bad-alloc-heavy-industries/SPIFlashProgrammer/firmware/TivaC/Startup.c

/*
 * This file is part of SPI Flash Programmer (SPIFP)
 * Copyright © 2014 Rachel Mant (dx-mon@users.sourceforge.net)
 *
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
 * You should have received a copy of the GNU General Public License
 * along with this program.  If not, see <http://www.gnu.org/licenses/>.
 */

/* The startup code for the TivaC */
#include <stdint.h>

#ifndef NULL
#define NULL	(void *)0
#endif

extern int main();
void irqReset();
void irqNMI();
void irqEmptyDef();
void irqHardFault() __attribute__((naked));

extern uint32_t _stack_top;
extern uint32_t _start_text, _end_text;
extern uint32_t _start_data, _end_data;
extern uint32_t _start_bss, _end_bss;

typedef void (*irqFunction)();
irqFunction vectorTable[] __attribute__((section(".nvic_table"))) =
{
	(irqFunction)&_stack_top, /* Startup value for stack pointer */
	irqReset, /* Reset handler */
	irqNMI, /* NMI handler */
	irqHardFault, /* Hard Fault handler */

	/* Configurable priority handlers */
	irqEmptyDef, /* MMU Fault handler */
	irqEmptyDef, /* Bus Fault handler */
	irqEmptyDef, /* Usage Fault */
	NULL, /* Reserved */
	NULL, /* Reserved */
	NULL, /* Reserved */
	NULL, /* Reserved */
	irqEmptyDef, /* SV Call */
	irqEmptyDef, /* Debug Monitor */
	NULL, /* Reserved */
	irqEmptyDef, /* Pending SV */
	irqEmptyDef, /* Sys Tick */

	/* Peripheral handlers */
	irqEmptyDef, /* GPIO Port A */
	irqEmptyDef, /* GPIO Port B */
	irqEmptyDef, /* GPIO Port C */
	irqEmptyDef, /* GPIO Port D */
	irqEmptyDef, /* GPIO Port E */
	irqEmptyDef, /* UART 0 */
	irqEmptyDef, /* UART 1 */
	irqEmptyDef, /* SSI 0 */
	irqEmptyDef, /* I2C 0 */
	irqEmptyDef, /* PWM 0 Fault */
	irqEmptyDef, /* PWM 0 Gen 0 */
	irqEmptyDef, /* PWM 0 Gen 1 */
	irqEmptyDef, /* PWM 0 Gen 2 */
	irqEmptyDef, /* QEI 0 */
	irqEmptyDef, /* ADC 0 Seq 0 */
	irqEmptyDef, /* ADC 0 Seq 1 */
	irqEmptyDef, /* ADC 0 Seq 2 */
	irqEmptyDef, /* ADC 0 Seq 3 */
	irqEmptyDef, /* WDT 0 and 1 */
	irqEmptyDef, /* Timer 0 A (16/32-bit) */
	irqEmptyDef, /* Timer 0 B (16/32-bit) */
	irqEmptyDef, /* Timer 1 A (16/32-bit) */
	irqEmptyDef, /* Timer 1 B (16/32-bit) */
	irqEmptyDef, /* Timer 2 A (16/32-bit) */
	irqEmptyDef, /* Timer 2 B (16/32-bit) */
	irqEmptyDef, /* Analog Comparator 0 */
	irqEmptyDef, /* Analog Comparator 1 */
	NULL, /* Reserved */
	irqEmptyDef, /* SysCtl */
	irqEmptyDef, /* Flash + EEPROM Ctl */
	irqEmptyDef, /* GPIO Port F */
	NULL, /* Reserved */
	NULL, /* Reserved */
	irqEmptyDef, /* UART 2 */
	irqEmptyDef, /* SSI 1 */
	irqEmptyDef, /* Timer 3 A (16/32-bit) */
	irqEmptyDef, /* Timer 3 B (16/32-bit) */
	irqEmptyDef, /* I2C 1 */
	irqEmptyDef, /* QEI 1 */
	irqEmptyDef, /* CAN 0 */
	NULL, /* Reserved */
	NULL, /* Reserved */
	NULL, /* Reserved */
	irqEmptyDef, /* Hibernation Module */
	irqEmptyDef, /* USB */
	NULL, /* Reserved */
	irqEmptyDef, /* UDMA SW */
	irqEmptyDef, /* UDMA Error */
	irqEmptyDef, /* ADC 1 Seq 0 */
	irqEmptyDef, /* ADC 1 Seq 1 */
	irqEmptyDef, /* ADC 1 Seq 2 */
	irqEmptyDef, /* ADC 1 Seq 3 */
	NULL, /* Reserved */
	NULL, /* Reserved */
	NULL, /* Reserved */
	NULL, /* Reserved */
	NULL, /* Reserved */
	irqEmptyDef, /* SSI 2 */
	irqEmptyDef, /* SSI 3 */
	irqEmptyDef, /* UART 3 */
	irqEmptyDef, /* UART 4 */
	irqEmptyDef, /* UART 5 */
	irqEmptyDef, /* UART 6 */
	irqEmptyDef, /* UART 7 */
	NULL, /* Reserved */
	NULL, /* Reserved */
	NULL, /* Reserved */
	NULL, /* Reserved */
	irqEmptyDef, /* I2C 2 */
	irqEmptyDef, /* I2C 4 */
	irqEmptyDef, /* Timer 4 A (16/32-bit) */
	irqEmptyDef, /* Timer 4 B (16/32-bit) */
	NULL, /* Reserved */
	NULL, /* Reserved */
	NULL, /* Reserved */
	NULL, /* Reserved */
	NULL, /* Reserved */
	NULL, /* Reserved */
	NULL, /* Reserved */
	NULL, /* Reserved */
	NULL, /* Reserved */
	NULL, /* Reserved */
	NULL, /* Reserved */
	NULL, /* Reserved */
	NULL, /* Reserved */
	NULL, /* Reserved */
	NULL, /* Reserved */
	NULL, /* Reserved */
	NULL, /* Reserved */
	NULL, /* Reserved */
	NULL, /* Reserved */
	NULL, /* Reserved */
	irqEmptyDef, /* Timer 5 A (16/32-bit) */
	irqEmptyDef, /* Timer 5 B (16/32-bit) */
	irqEmptyDef, /* Timer 0 A (32/64-bit) */
	irqEmptyDef, /* Timer 0 B (32/64-bit) */
	irqEmptyDef, /* Timer 1 A (32/64-bit) */
	irqEmptyDef, /* Timer 1 B (32/64-bit) */
	irqEmptyDef, /* Timer 2 A (32/64-bit) */
	irqEmptyDef, /* Timer 2 B (32/64-bit) */
	irqEmptyDef, /* Timer 3 A (32/64-bit) */
	irqEmptyDef, /* Timer 3 B (32/64-bit) */
	irqEmptyDef, /* Timer 4 A (32/64-bit) */
	irqEmptyDef, /* Timer 4 B (32/64-bit) */
	irqEmptyDef, /* Timer 5 A (32/64-bit) */
	irqEmptyDef, /* Timer 5 B (32/64-bit) */
	irqEmptyDef, /* System Exception */
	NULL, /* Reserved */
	NULL, /* Reserved */
	NULL, /* Reserved */
	NULL, /* Reserved */
	NULL, /* Reserved */
	NULL, /* Reserved */
	NULL, /* Reserved */
	NULL, /* Reserved */
	NULL, /* Reserved */
	NULL, /* Reserved */
	NULL, /* Reserved */
	NULL, /* Reserved */
	NULL, /* Reserved */
	NULL, /* Reserved */
	NULL, /* Reserved */
	NULL, /* Reserved */
	NULL, /* Reserved */
	NULL, /* Reserved */
	NULL, /* Reserved */
	NULL, /* Reserved */
	NULL, /* Reserved */
	NULL, /* Reserved */
	NULL, /* Reserved */
	NULL, /* Reserved */
	NULL, /* Reserved */
	NULL, /* Reserved */
	NULL, /* Reserved */
	NULL, /* Reserved */
	NULL, /* Reserved */
	NULL, /* Reserved */
	NULL, /* Reserved */
	NULL /* Reserved */
};

void irqReset()
{
	uint32_t *src, *dst;

	while (1)
	{
		src = &_end_text;
		dst = &_start_data;
		while (dst < &_end_data)
			*dst++ = *src++;

		dst = &_start_bss;
		while (dst < &_end_bss)
			*dst++ = 0;

		main();
	}
}

void irqNMI()
{
	while (1);
}

void irqHardFault()
{
	/* Get some information about the fault for the debugger.. */
	__asm__("	movs	r0, #4\n"
		"	movs	r1, lr\n"
		"	tst		r0, r1\n"
		"	beq		_MSP\n"
		"	mrs		r0, psp\n"
		"	b		_HALT\n"
		"_MSP:\n"
		"	mrs		r0, msp\n"
		"_HALT:\n"
		"	ldr		r1, [r0, 0x00]\n" /* r0 */
		"	ldr		r2, [r0, 0x04]\n" /* r1 */
		"	ldr		r3, [r0, 0x08]\n" /* r2 */
		"	ldr		r4, [r0, 0x0C]\n" /* r3 */
		"	ldr		r5, [r0, 0x10]\n" /* r12 */
		"	ldr		r6, [r0, 0x14]\n" /* lr */
		"	ldr		r7, [r0, 0x18]\n" /* pc */
		"	ldr		r8, [r0, 0x1C]\n" /* xpsr */
		"	bkpt	#0\n");
	/* The lowest 8 bits of r8 (xpsr) contain which handler triggered this, if there is a signal handler frame before this. */

	while (1);
}

void irqEmptyDef()
{
	while (1);
}
