bad-alloc-heavy-industries/SPIFlashProgrammer/firmware/LPC4370/USBTypes.h

/*
 * This file is part of SPI Flash Programmer (SPIFP)
 * Copyright © 2014 Rachel Mant (dx-mon@users.sourceforge.net)
 *
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
 * You should have received a copy of the GNU General Public License
 * along with this program.  If not, see <http://www.gnu.org/licenses/>.
 */

#ifndef USBTypes_H
#define USBTypes_H

/*
 * Definition of naming conventions used:
 * EP => EndPoint
 * BDT => Buffer Descriptor Table
 * TD => Transfer Descriptor
 * PID => Packet ID
 */

#define USB_ENDPOINTS				6
#define USB_BDT_ENTRIES				12
#define USB_BTD_ADDR				__attribute__((aligned(2048)))
#define USB_TD_ALIGN				__attribute__((aligned(32)))

#define USB_EP0_SETUP_LEN			8
#define USB_EP0_SETUP_ADDR			__attribute__((aligned(8)))
#define USB_EP0_DATA_LEN			8
#define USB_EP0_DATA_ADDR			__attribute__((aligned(8)))

#define USB_EP1_OUT_LEN				64
#define USB_EP1_OUT_ADDR			__attribute__((aligned(64)))
#define USB_EP1_IN_LEN				64
#define USB_EP1_IN_ADDR				__attribute__((aligned(64)))

#define USB_EP2_IN_LEN				64
#define USB_EP2_IN_ADDR				__attribute__((aligned(64)))

#define USB_DIR_OUT					0
#define USB_DIR_IN					1

#define USB_DEFER_STATUS_PACKETS	0x01
#define USB_DEFER_IN_PACKETS		0x02
#define USB_DEFER_OUT_PACKETS		0x04

#define USB_BUFFER_SRC_MEM			0
#define USB_BUFFER_SRC_FLASH		1

#define USB_STATUS_TIMEOUT			45

#define USB_EPCAP_IOS				0x00008000
#define USB_EPCAP_LEN_MASK			0x07FF0000
#define USB_EPCAP_ZLT				0x20000000
#define USB_EPCAP_MULT_MASK			0xC0000000
#define USB_EPCAP_MULT_1			0x40000000
#define USB_EPCAP_MULT_2			0x80000000
#define USB_EPCAP_MULT_3			0xC0000000

#define USB_TD_STATUS_MASK			0x000000FF
#define USB_TD_MULTO_MASK			0x00000C00
#define USB_TD_IOC					0x00008000
#define USB_TD_COUNT_MASK			0x7FFF0000
#define USB_INVALID_TD				(void *)0x00000001

#define USB_PAGE_MASK				0xFFFFF000
#define USB_PAGE_INC				0x00001000

#define nullptr						((void *)0)

typedef union
{
	uint8_t value;
	struct
	{
		uint8_t bdtIndex : 5;
		uint8_t : 3;
	};
	struct
	{
		uint8_t dir : 1;
		uint8_t epNum : 4;
		uint8_t buff : 1;
		uint8_t : 2;
	};
} usbEP_t;

typedef struct
{
	uint8_t length;
	const void *descriptor;
} usbMultiPartDesc_t;

typedef struct
{
	uint8_t numDesc;
	const usbMultiPartDesc_t *descriptors;
} usbMultiPartTable_t;

typedef struct
{
	union
	{
		uint8_t value;
		struct
		{
			uint8_t needsArming : 1;
			uint8_t buffSrc : 1;
			uint8_t multiPart : 1;
			uint8_t part : 4;
		};
	};
	union
	{
		volatile void *memPtr;
		const void *flashPtr;
		uint8_t *memBuff;
		const uint8_t *flashBuff;
	} buffer;
	usbEP_t ep;
	uint16_t xferCount;
	uint16_t epLen;
	uint8_t partCount;
	const usbMultiPartTable_t *partDesc;
	void (*func)();
} usbEPStatus_t;

typedef struct usbTD_t
{
	volatile struct usbTD_t *nextTD;
	uint32_t status;
	union
	{
		volatile void *buffer0;
		uint32_t bufferOffset : 12;
	};
	union
	{
		volatile void *buffer1;
		uint32_t frameNumber : 11;
	};
	volatile void *buffer2;
	volatile void *buffer3;
	volatile void *buffer4;
	uint32_t reserved1;
} usbTD_t;

typedef struct
{
	union
	{
		uint8_t value;
		struct
		{
			uint8_t recipient : 5;
			uint8_t type : 2;
			uint8_t direction : 1;
		};
	} requestType;
	uint8_t request;
	union
	{
		uint16_t value;
		struct
		{
			uint8_t index;
			uint8_t type;
		} descriptor;
		struct
		{
			uint8_t addrL;
			uint8_t addrH;
		} address;
		struct
		{
			uint8_t value;
			uint8_t reserved;
		} config;
		struct
		{
			uint8_t value;
			uint8_t reserved;
		} feature;
	} value;
	union
	{
		uint16_t value;
		struct
		{
			uint8_t epNum : 4;
			uint8_t : 3;
			uint8_t epDir : 1;
			uint8_t : 8;
		};
	} index;
	uint16_t length;
} usbSetupPacket_t;

typedef struct
{
	uint32_t epCaps;
	usbTD_t *activeHwTD;
	usbTD_t activeTD;
	usbSetupPacket_t setupPacket;
	uint32_t reserved[4];
} usbBDTEntry_t;

typedef enum
{
	USB_CTRL_STATE_WAIT,
	USB_CTRL_STATE_TX,
	USB_CTRL_STATE_RX
} usbCtrlState_t;

typedef enum
{
	USB_STATE_DETACHED,
	USB_STATE_ATTACHED,
	USB_STATE_POWERED,
	USB_STATE_WAITING,
	USB_STATE_ADDRESSED,
	USB_STATE_CONFIGURED
} usbDeviceState;

typedef enum
{
	USB_PID_NONE,
	USB_PID_OUT,
	USB_PID_ACK,
	USB_PID_DATA0,
	USB_PID_PING,
	USB_PID_SOF,
	USB_PID_NYET,
	USB_PID_DATA2,
	USB_PID_SPLIT,
	USB_PID_IN,
	USB_PID_NAK,
	USB_PID_DATA1,
	USB_PID_PRE_ERROR,
	USB_PID_SETUP,
	USB_PID_STALL,
	USB_PID_MDATA
} usbPID_t;

typedef enum
{
	USB_REQUEST_GET_STATUS = 0,
	USB_REQUEST_CLEAR_FEATURE = 1,
	USB_REQUEST_SET_FEATURE = 3,
	USB_REQUEST_SET_ADDRESS = 5,
	USB_REQUEST_GET_DESCRIPTOR = 6,
	USB_REQUEST_SET_DESCRIPTOR = 7,
	USB_REQUEST_GET_CONFIGURATION = 8,
	USB_REQUEST_SET_CONFIGURATION = 9,
	USB_REQUEST_GET_INTERFACE = 10,
	USB_REQUEST_SET_INTERFACE = 11,
	USB_REQUEST_SYNC_FRAME = 12
} usbRequest_t;

typedef enum
{
	USB_REQUEST_TYPE_STANDARD,
	USB_REQUEST_TYPE_CLASS,
	USB_REQUEST_TYPE_VENDOR,
	USB_REQUEST_TYPE_RESERVED
} usbRequestType_t;

typedef enum
{
	USB_RECIPIENT_DEVICE,
	USB_RECIPIENT_INTERFACE,
	USB_RECIPIENT_ENDPOINT,
	USB_RECIPIENT_OTHER,
	USB_RECIPIENT_RESERVED
} usbRecipient_t;

typedef enum
{
	USB_FEATURE_ENDPOINT_STALL,
	USB_FEATURE_REMOTE_WAKEUP,
	USB_FEATURE_TEST_MODE
} usbFeature_t;

typedef enum
{
	USB_STALL_STATE_IDLE,
	USB_STALL_STATE_ARM,
	USB_STALL_STATE_STALL
} usbStallState_t;

#define USB_CONF_ATTR_DEFAULT	0x80
#define USB_CONF_ATTR_SELFPWR	0x40
#define USB_CONF_ATTR_RWU		0x20
#define USB_CONF_ATTR_HNP		0x02
#define USB_CONF_ATTR_SRP		0x01

#define USB_CLASS_COMMS			0x02
#define USB_CLASS_DATA			0x0A
#define USB_CLASS_MSD			0x08
#define USB_CLASS_VENDOR		0xFF

#define USB_SUBCLASS_NONE		0x00
#define USB_SUBCLASS_ACM		0x02
#define USB_SUBCLASS_MSD		0x06
#define USB_SUBCLASS_VENDOR		0xFF

#define USB_PROTOCOL_NONE		0x00
#define USB_PROTOCOL_V25_AT		0x01
#define USB_PROTOCOL_TRANS		0x32
#define USB_PROTOCOL_BULK_ONLY	0x50
#define USB_PROTOCOL_CDC		0xFE
#define USB_PROTOCOL_VENDOR		0xFF

#define USB_EPTYPE_CTRL			0x00
#define USB_EPTYPE_ISO			0x01
#define USB_EPTYPE_BULK			0x02
#define USB_EPTYPE_INTR			0x03

typedef struct
{
	uint8_t length;
	uint8_t descriptorType;
	uint16_t usbVersion;
	uint8_t deviceClass;
	uint8_t deviceSubClass;
	uint8_t devicePRotocol;
	uint8_t maxPacketSize0;
	uint16_t vendorID;
	uint16_t productID;
	uint16_t deviceVersion;
	uint8_t strMfrIndex;
	uint8_t strProductIndex;
	uint8_t strSerialNoIndex;
	uint8_t numConfigurations;
} usbDeviceDescriptor_t;

typedef struct
{
	uint8_t length;
	uint8_t descriptorType;
	uint16_t totalLength;
	uint8_t numInterfaces;
	uint8_t configurationValue;
	uint8_t strConfigurationIndex;
	uint8_t attributes;
	uint8_t maxPower;
} usbConfigDescriptor_t;

typedef struct
{
	uint8_t length;
	uint8_t descriptorType;
	uint8_t interfaceNumber;
	uint8_t alternateSetting;
	uint8_t numEndpoints;
	uint8_t interfaceClass;
	uint8_t interfaceSubClass;
	uint8_t interfaceProtocol;
	uint8_t strInterfaceIdx;
} usbInterfaceDescriptor_t;

typedef struct
{
	uint8_t length;
	uint8_t descriptorType;
	uint8_t endpointAddress;
	uint8_t attributes;
	uint16_t maxPacketSize;
	uint8_t interval;
} usbEndpointDescriptor_t;

typedef struct
{
	uint8_t length;
	uint8_t descriptorType;
} usbStringDescBase_t;

typedef struct
{
	uint8_t length;
	uint8_t descriptorType;
	uint8_t firstInterface;
	uint8_t interfaceCount;
	uint8_t functionClass;
	uint8_t functionSubClass;
	uint8_t functionProtocol;
	uint8_t iFunction;
} usbInterfaceAssocDescriptor_t;

typedef enum
{
	USB_DESCRIPTOR_INVALID,
	USB_DESCRIPTOR_DEVICE,
	USB_DESCRIPTOR_CONFIGURATION,
	USB_DESCRIPTOR_STRING,
	USB_DESCRIPTOR_INTERFACE,
	USB_DESCRIPTOR_ENDPOINT,
	USB_DESCRIPTOR_DEVICE_QUALIFIER,
	USB_DESCRIPTOR_OTHER_SPEED,
	USB_DESCRIPTOR_INTERFACE_POWER,
	USB_DESCRIPTOR_OTG,
	USB_DESCRIPTOR_DEBUG,
	USB_DESCRIPTOR_INTERFACE_ASSOCIATION
} usbDescriptor_t;

extern usbEPStatus_t usbStatusInEP[USB_ENDPOINTS];
extern usbEPStatus_t usbStatusOutEP[USB_ENDPOINTS];
extern volatile usbBDTEntry_t usbBDT[USB_BDT_ENTRIES];
extern volatile uint8_t usbEP0Data[USB_EP0_DATA_LEN];

#endif /*USBTypes_H*/
